Ashington258/EquiCycle/struct/打印件/打印件2022/8活口卡件.STL

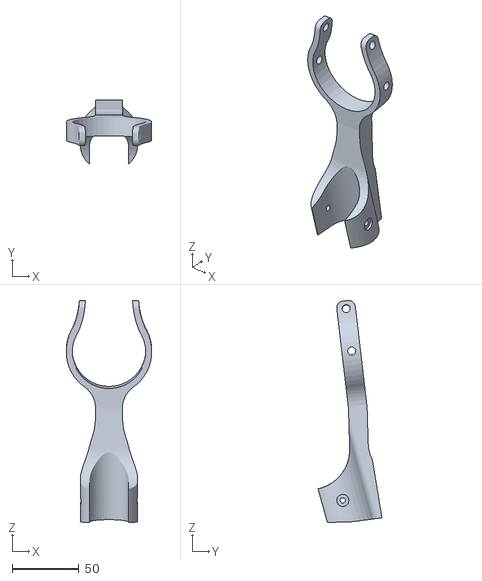
[picture p37: CAD file, 2024-12-03]
struct/打印件/打印件2022/8活口卡件.STL
64.0 x 47.9 x 166.2
