Ashington258/EquiCycle/struct/打印件/打印件2023/02 舵机/17 车把.STL

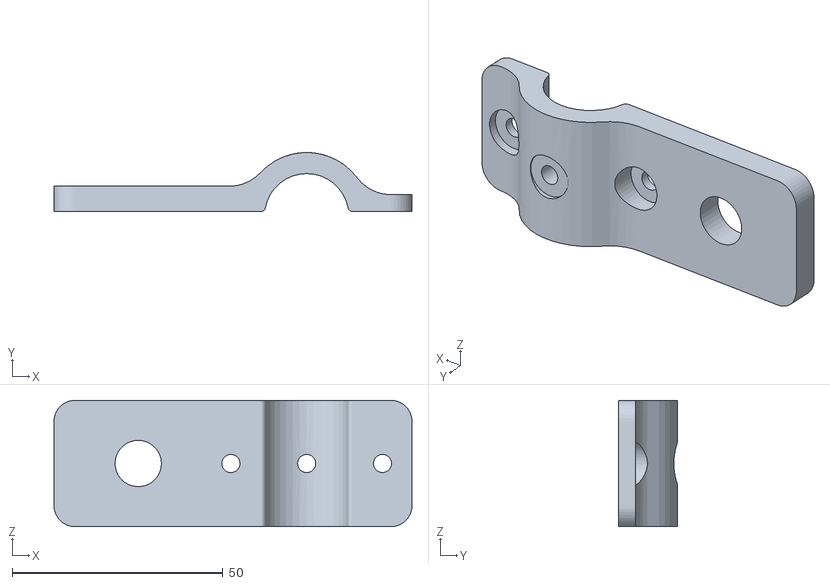
[picture p38: CAD file, 2024-12-03]
struct/打印件/打印件2023/02 舵机/17 车把.STL
85.0 x 14.0 x 30.0
