Ashington258/EquiCycle/struct/打印件/打印件2023/05 动量轮部分/10轴套_4个.STL

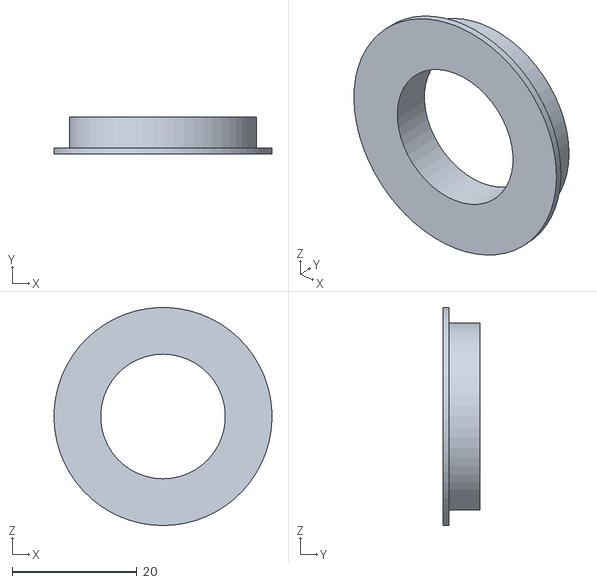
[picture p39: CAD file, 2024-12-03]
struct/打印件/打印件2023/05 动量轮部分/10轴套_4个.STL
35.0 x 6.00 x 35.0
