Ashington258/EquiCycle/struct/打印件/打印件2022/06动量驱动定子_φ6.STL

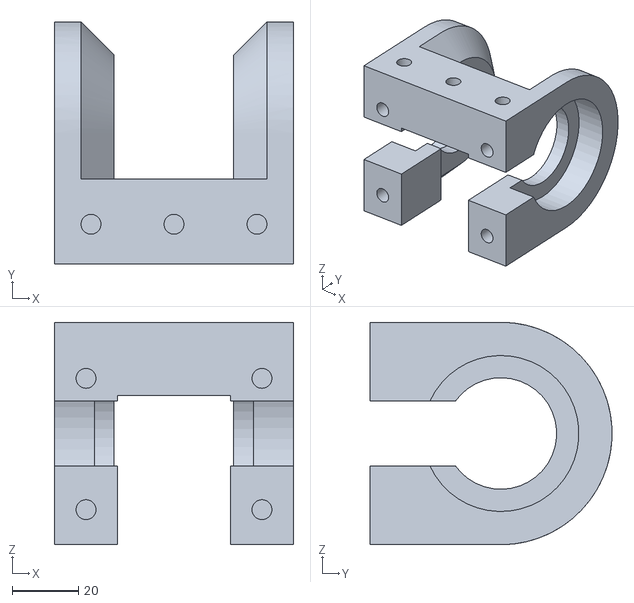
[picture p40: CAD file, 2024-12-03]
struct/打印件/打印件2022/06动量驱动定子_φ6.STL
72.0 x 72.9 x 67.0
