Ashington258/EquiCycle/struct/打印件/打印件2023/05 动量轮部分/05 动量轮定子.STL

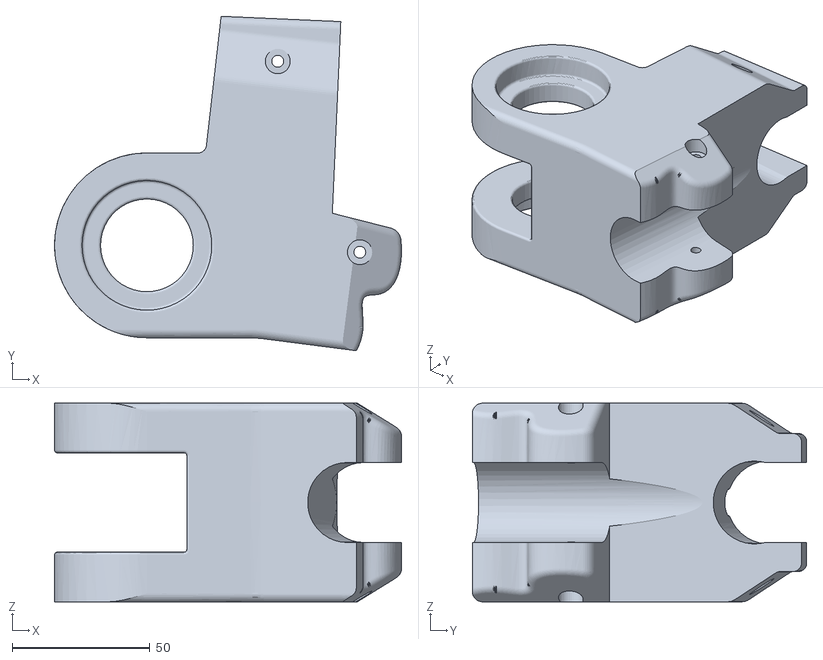
[picture p41: CAD file, 2024-12-03]
struct/打印件/打印件2023/05 动量轮部分/05 动量轮定子.STL
125.8 x 121.2 x 72.0
