Ashington258/EquiCycle/struct/打印件/打印件2023/05 动量轮部分/08活口卡件1.STL

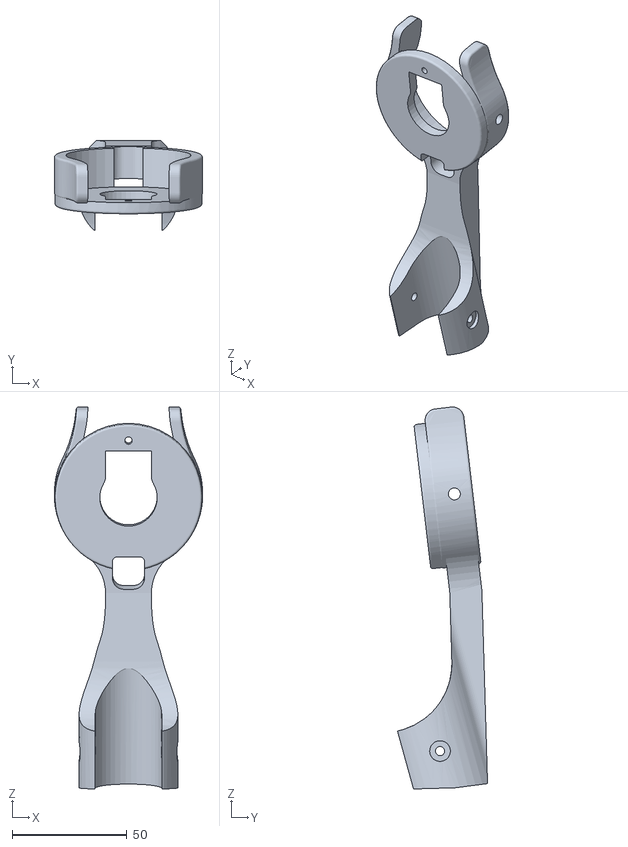
[picture p42: CAD file, 2024-12-03]
struct/打印件/打印件2023/05 动量轮部分/08活口卡件1.STL
64.5 x 39.2 x 166.3
