Ashington258/EquiCycle/struct/打印件/打印件2022/10后轮驱动定子1.STL

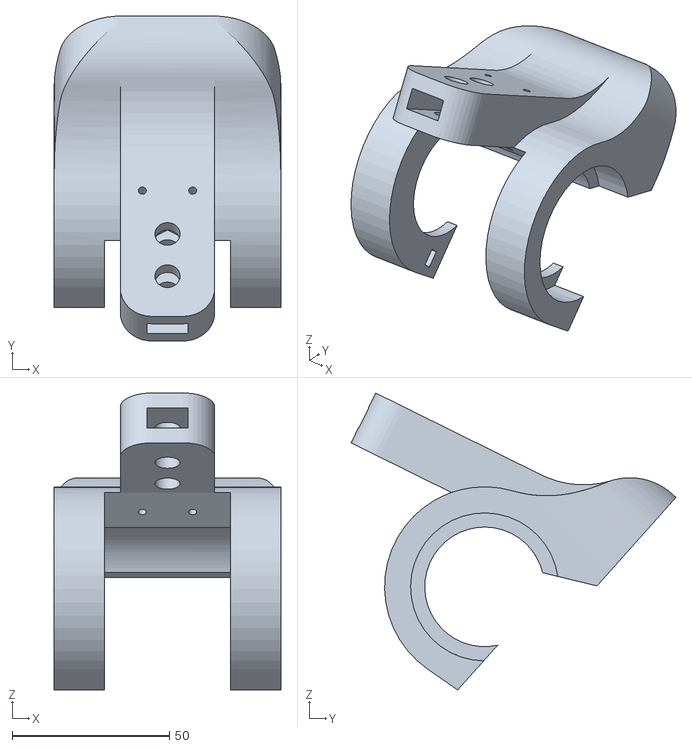
[picture p43: CAD file, 2024-12-03]
struct/打印件/打印件2022/10后轮驱动定子1.STL
72.0 x 103.3 x 94.3
