Ashington258/EquiCycle/struct/打印件/打印件2023/05 动量轮部分/07 转子轴.STL

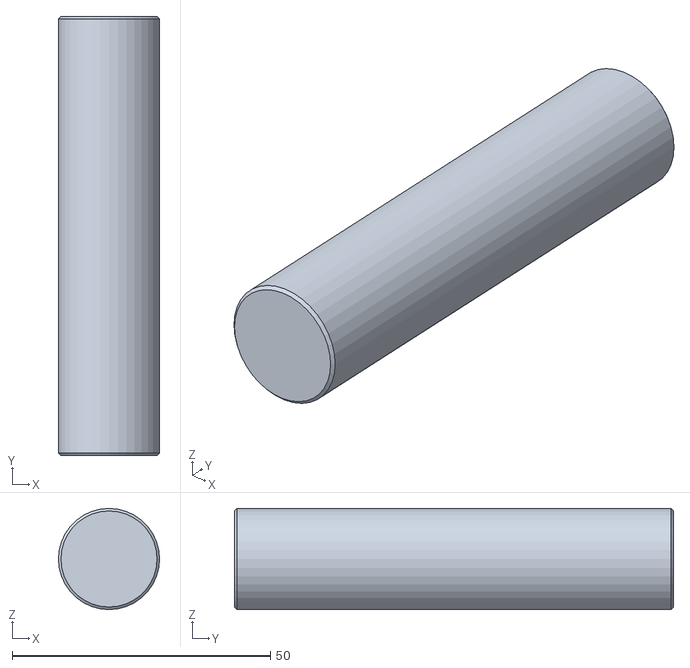
[picture p44: CAD file, 2024-12-03]
struct/打印件/打印件2023/05 动量轮部分/07 转子轴.STL
19.6 x 85.0 x 19.6
