Ashington258/EquiCycle/struct/打印件/打印件2022/07动量驱动动子.stl

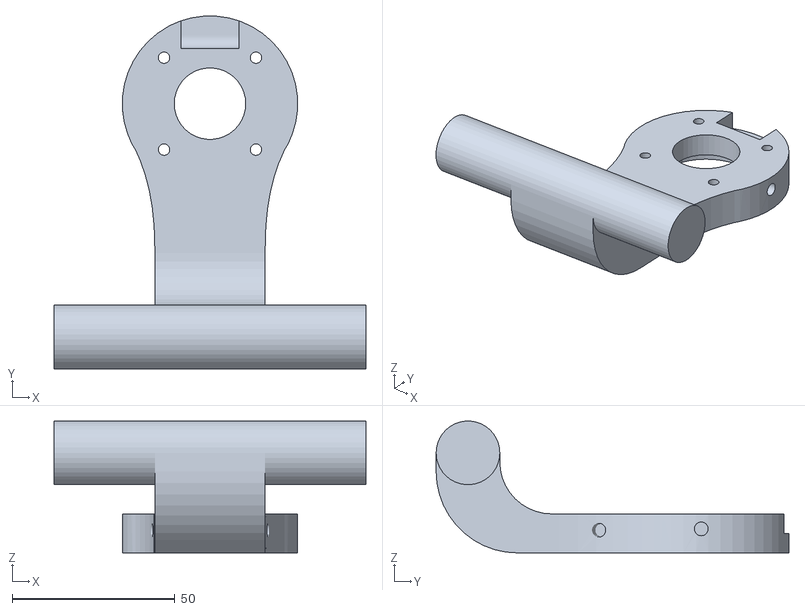
[picture p45: CAD file, 2024-12-03]
struct/打印件/打印件2022/07动量驱动动子.stl
96.0 x 108.5 x 40.6
