Ashington258/EquiCycle/struct/打印件/打印件2022/05固定架.STL

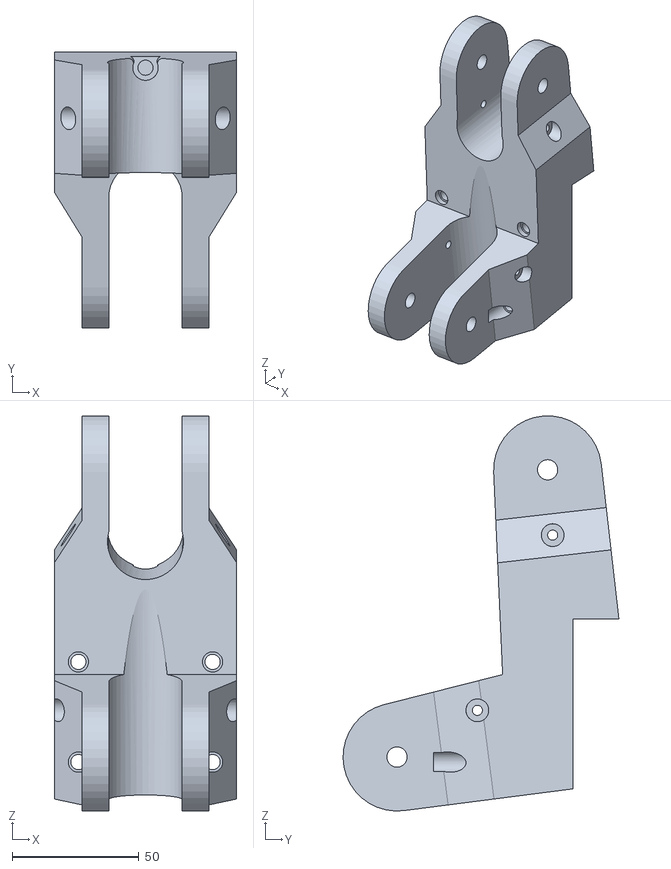
[picture p46: CAD file, 2024-12-03]
struct/打印件/打印件2022/05固定架.STL
72.0 x 109.0 x 156.0
